ngai-jeremy/WeatherPaper/Firmware/bitmaps.h

#ifndef BITMAPS_H
#define BITMAPS_H

#include <Arduino.h>

const unsigned char epd_bitmap_broken_clouds[] PROGMEM = {
  0x00, 0x00, 0x00, 0x00, 0x00, 0x00, 0x00, 0x00, 0x00, 0x00, 0x00, 0x00, 0x00, 0x00, 0x00, 0x00,
  0x00, 0x00, 0x00, 0x00, 0x00, 0x00, 0x00, 0x00, 0x00, 0x00, 0x00, 0x00, 0x00, 0x00, 0x00, 0x00,
  0x00, 0x00, 0x00, 0x00, 0x00, 0x00, 0x00, 0x00, 0x00, 0x00, 0x00, 0x00, 0x00, 0x00, 0x00, 0x00,
  0x00, 0x00, 0x00, 0x00, 0x00, 0x00, 0x00, 0x00, 0x00, 0x00, 0x00, 0x00, 0x00, 0x00, 0x00, 0x00,
  0x00, 0x00, 0x00, 0x00, 0x00, 0x00, 0x00, 0x00, 0x00, 0x00, 0x00, 0x00, 0x00, 0x00, 0x00, 0x00,
  0x00, 0x00, 0x00, 0x00, 0x00, 0x00, 0x00, 0x00, 0x00, 0x00, 0x00, 0x00, 0x00, 0x00, 0x00, 0x00,
  0x00, 0x00, 0x00, 0x00, 0x00, 0x00, 0x00, 0x00, 0x00, 0x00, 0x00, 0x00, 0x3f, 0xc0, 0x00, 0x00,
  0x00, 0x00, 0x00, 0x01, 0xff, 0xf8, 0x00, 0x00, 0x00, 0x00, 0x00, 0x07, 0xff, 0xfc, 0x00, 0x00,
  0x00, 0x00, 0x00, 0x0f, 0xff, 0xff, 0x00, 0x00, 0x00, 0x00, 0x00, 0x1f, 0xc0, 0x3f, 0x80, 0x00,
  0x00, 0x00, 0x00, 0x3f, 0x00, 0x0f, 0xc0, 0x00, 0x00, 0x00, 0x00, 0x7c, 0x00, 0x03, 0xe0, 0x00,
  0x00, 0x00, 0x00, 0xfc, 0x00, 0x01, 0xe0, 0x00, 0x00, 0x00, 0x0f, 0xff, 0x00, 0x01, 0xf0, 0x00,
  0x00, 0x00, 0x3f, 0xff, 0xc0, 0x00, 0xff, 0x80, 0x00, 0x00, 0x7f, 0xff, 0xe0, 0x00, 0x7f, 0xe0,
  0x00, 0x00, 0xfe, 0x07, 0xf0, 0x00, 0x7f, 0xf0, 0x00, 0x01, 0xf8, 0x01, 0xf8, 0x00, 0x3f, 0xf8,
  0x00, 0x03, 0xe0, 0x00, 0x7c, 0x00, 0x00, 0x7c, 0x00, 0x07, 0xc0, 0x00, 0x3e, 0x00, 0x00, 0x3e,
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
  0xc7, 0x19, 0xd0, 0x61, 0x8c, 0x00, 0xfb, 0x8e, 0xd0, 0x61, 0x8c, 0x00, 0xc0, 0x00, 0xc0, 0x00, 0x00, 0x00, 0x80, 0x00, 0xc0, 0x00,
  0x00, 0x00, 0x80, 0x31, 0x80, 0x00, 0x00, 0x00, 0x00, 0x1f, 0x00, 0x00, 0x00, 0x00
};

#endif
