ngai-jeremy/WeatherPaper/Firmware/Petme8x8.h

#include <Adafruit_GFX.h>

const uint8_t Petme128Bitmaps[] PROGMEM = {
    0x00, 0x00, 0x00, 0x00, 0x00, 0x00, 0x00, 0x00, 0x18, 0x18, 0x18, 0x18,
    0x00, 0x00, 0x18, 0x00, 0x66, 0x66, 0x66, 0x00, 0x00, 0x00, 0x00, 0x00,
    0x66, 0x66, 0xFF, 0x66, 0xFF, 0x66, 0x66, 0x00, 0x18, 0x3E, 0x60, 0x3C,
    0x06, 0x7C, 0x18, 0x00, 0x62, 0x66, 0x0C, 0x18, 0x30, 0x66, 0x46, 0x00,
    0x3C, 0x66, 0x3C, 0x38, 0x67, 0x66, 0x3F, 0x00, 0x06, 0x0C, 0x18, 0x00,
    0x00, 0x00, 0x00, 0x00, 0x0C, 0x18, 0x30, 0x30, 0x30, 0x18, 0x0C, 0x00,
    0x30, 0x18, 0x0C, 0x0C, 0x0C, 0x18, 0x30, 0x00, 0x00, 0x66, 0x3C, 0xFF,
    0x3C, 0x66, 0x00, 0x00, 0x00, 0x18, 0x18, 0x7E, 0x18, 0x18, 0x00, 0x00,
    0x00, 0x00, 0x00, 0x00, 0x00, 0x18, 0x18, 0x30, 0x00, 0x00, 0x00, 0x7E,
    0x00, 0x00, 0x00, 0x00, 0x00, 0x00, 0x00, 0x00, 0x00, 0x18, 0x18, 0x00,
    0x00, 0x03, 0x06, 0x0C, 0x18, 0x30, 0x60, 0x00, 0x3C, 0x66, 0x6E, 0x76,
    0x66, 0x66, 0x3C, 0x00, 0x18, 0x18, 0x38, 0x18, 0x18, 0x18, 0x7E, 0x00,
    0x3C, 0x66, 0x06, 0x0C, 0x30, 0x60, 0x7E, 0x00, 0x3C, 0x66, 0x06, 0x1C,
    0x06, 0x66, 0x3C, 0x00, 0x06, 0x0E, 0x1E, 0x66, 0x7F, 0x06, 0x06, 0x00,
    0x7E, 0x60, 0x7C, 0x06, 0x06, 0x66, 0x3C, 0x00, 0x3C, 0x66, 0x60, 0x7C,
    0x66, 0x66, 0x3C, 0x00, 0x7E, 0x66, 0x0C, 0x18, 0x18, 0x18, 0x18, 0x00,
    0x3C, 0x66, 0x66, 0x3C, 0x66, 0x66, 0x3C, 0x00, 0x3C, 0x66, 0x66, 0x3E,
    0x06, 0x66, 0x3C, 0x00, 0x00, 0x00, 0x18, 0x00, 0x00, 0x18, 0x00, 0x00,
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
    {272, 8, 8, 8, 0, -8},
    {280, 8, 8, 8, 0, -8},
    {288, 8, 8, 8, 0, -8},
    {296, 8, 8, 8, 0, -8},
    {304, 8, 8, 8, 0, -8},
    {312, 8, 8, 8, 0, -8},
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
};

const GFXfont Petme8x8 PROGMEM = {
    (uint8_t *)Petme128Bitmaps,
    (GFXglyph *)Petme128Glyphs,
    0x20, 0x7E, 8};
